whqsz/ExpressLRS_DIY_Hardware/link/mlrs_.png

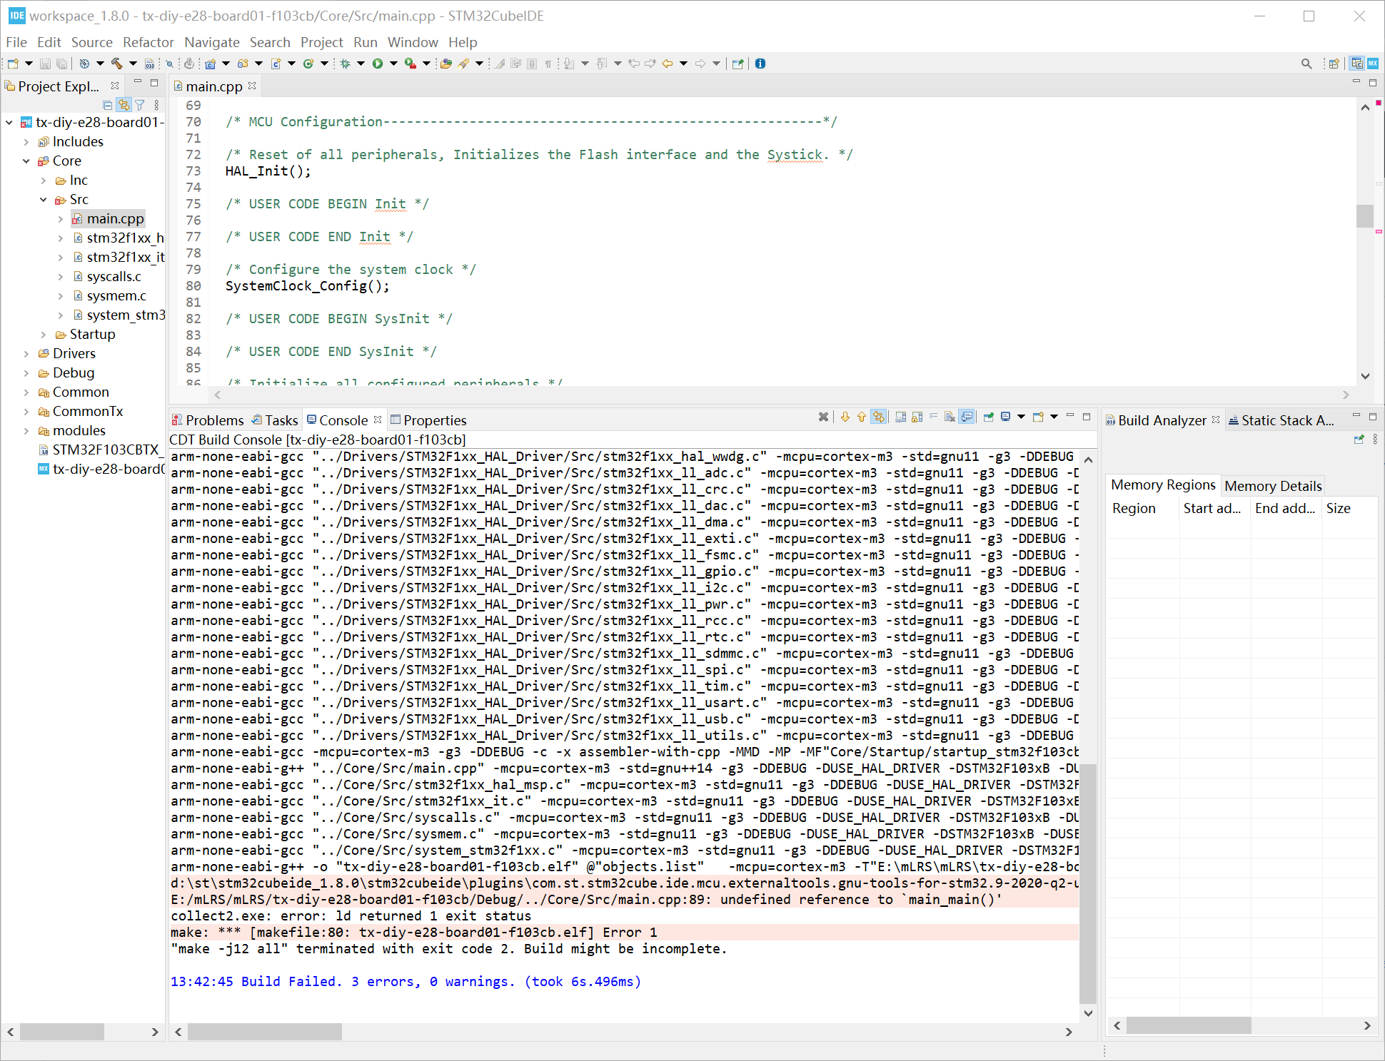
link/mlrs_.png
