whqsz/ExpressLRS_DIY_Hardware/RX-2G4-915M/2.4G/2.4_view.png

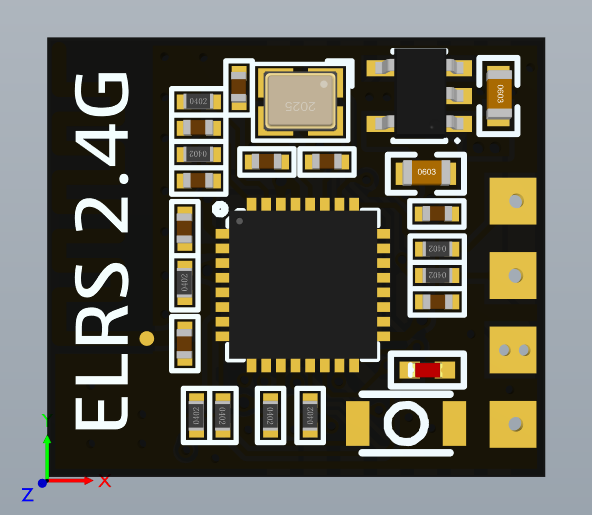
RX-2G4-915M/2.4G/2.4_view.png
