whqsz/ExpressLRS_DIY_Hardware/RX-2G4-915M/2.4G/焊接点位.png

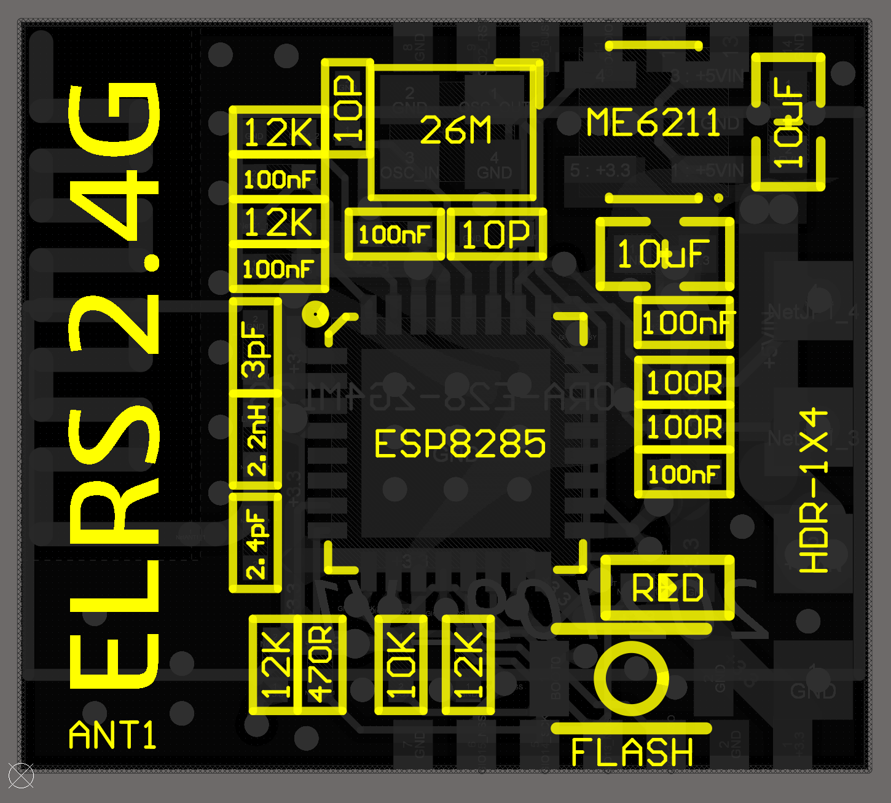
RX-2G4-915M/2.4G/焊接点位.png
