whqsz/ExpressLRS_DIY_Hardware/RX-2G4-915M/915M/E19-900M20S_ESP8285_CRSF_RX/915_view.png

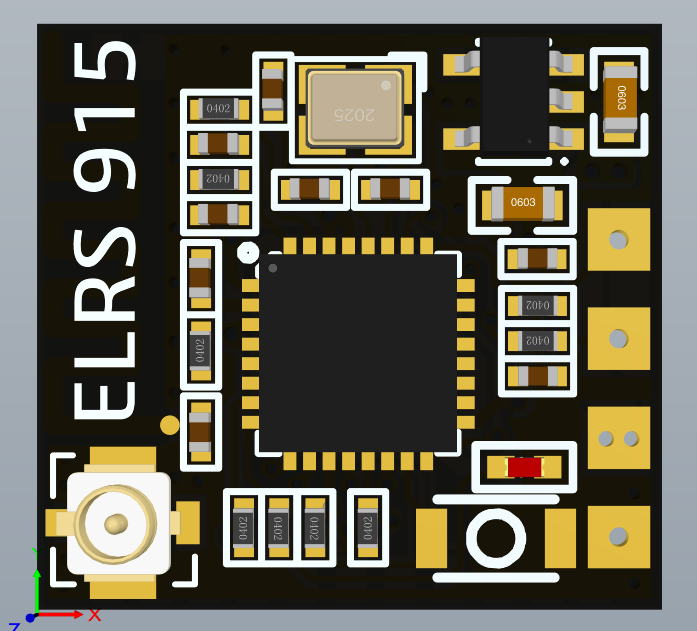
RX-2G4-915M/915M/E19-900M20S_ESP8285_CRSF_RX/915_view.png
