whqsz/ExpressLRS_DIY_Hardware/RX-2G4-915M/915M/E19-900M20S_ESP8285_PWM_RX/3D上.png

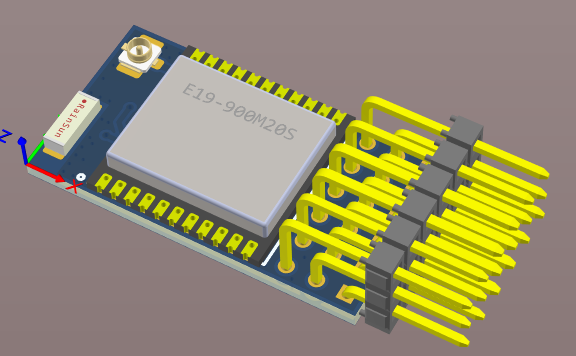
RX-2G4-915M/915M/E19-900M20S_ESP8285_PWM_RX/3D上.png
