whqsz/ExpressLRS_DIY_Hardware/RX-2G4-915M/915M/E32-900M20S_CRSF_RX/3D背.png

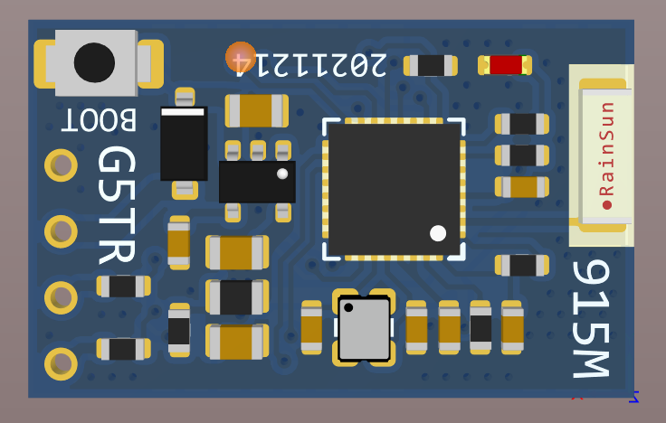
RX-2G4-915M/915M/E32-900M20S_CRSF_RX/3D背.png
