whqsz/ExpressLRS_DIY_Hardware/RX-2G4-915M/915M/E32-E900M20S_PWM_RX/3D正面.png

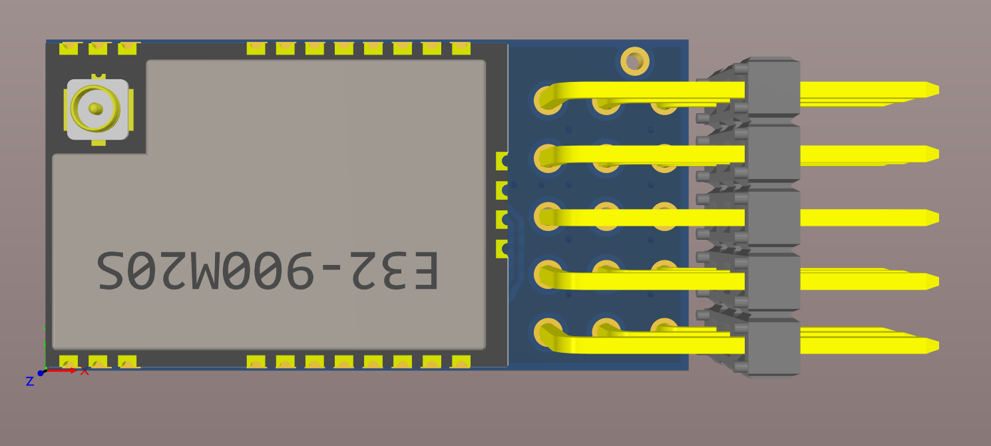
RX-2G4-915M/915M/E32-E900M20S_PWM_RX/3D正面.png
