whqsz/ExpressLRS_DIY_Hardware/TX/E19_915M_ESP32_2IN1_TX/2.4G模块引脚定义修改说明.png

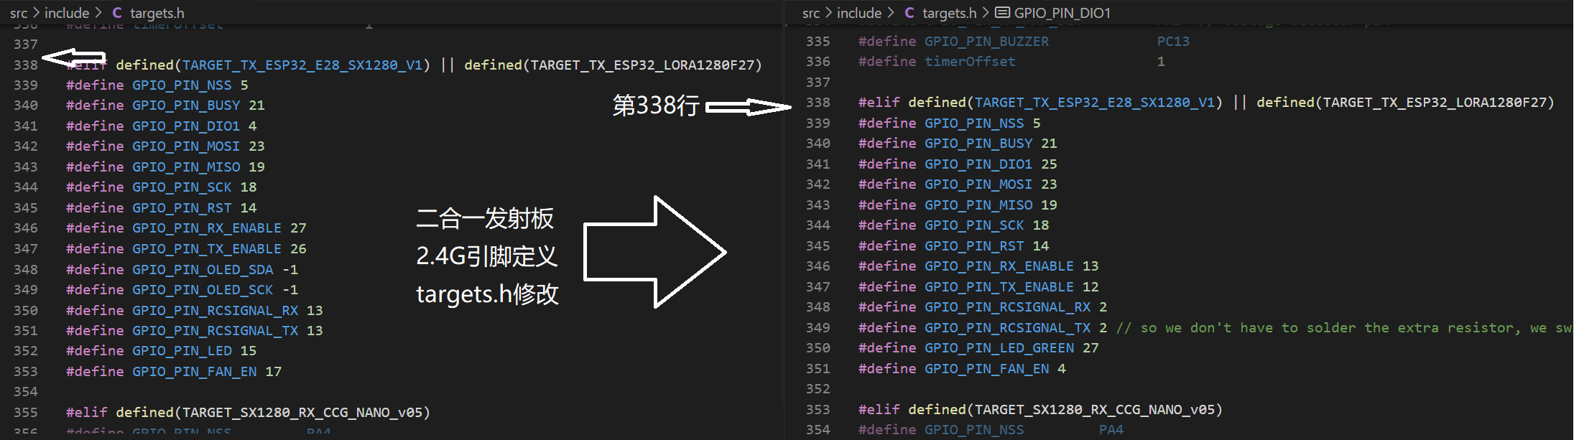
TX/E19_915M_ESP32_2IN1_TX/2.4G模块引脚定义修改说明.png
