whqsz/ExpressLRS_DIY_Hardware/TX/E19_915M_ESP32_2IN1_TX/3D背面.png

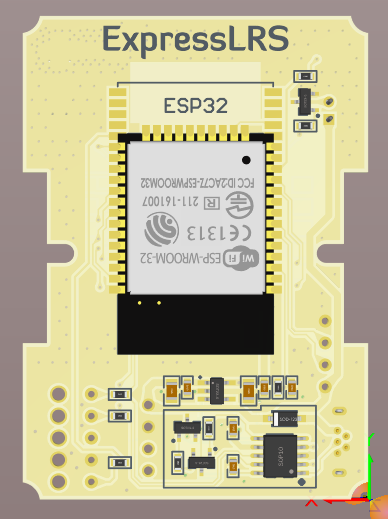
TX/E19_915M_ESP32_2IN1_TX/3D背面.png
