whqsz/ExpressLRS_DIY_Hardware/TX/E19_915M_ESP32_2IN1_TX/焊接点位正.png

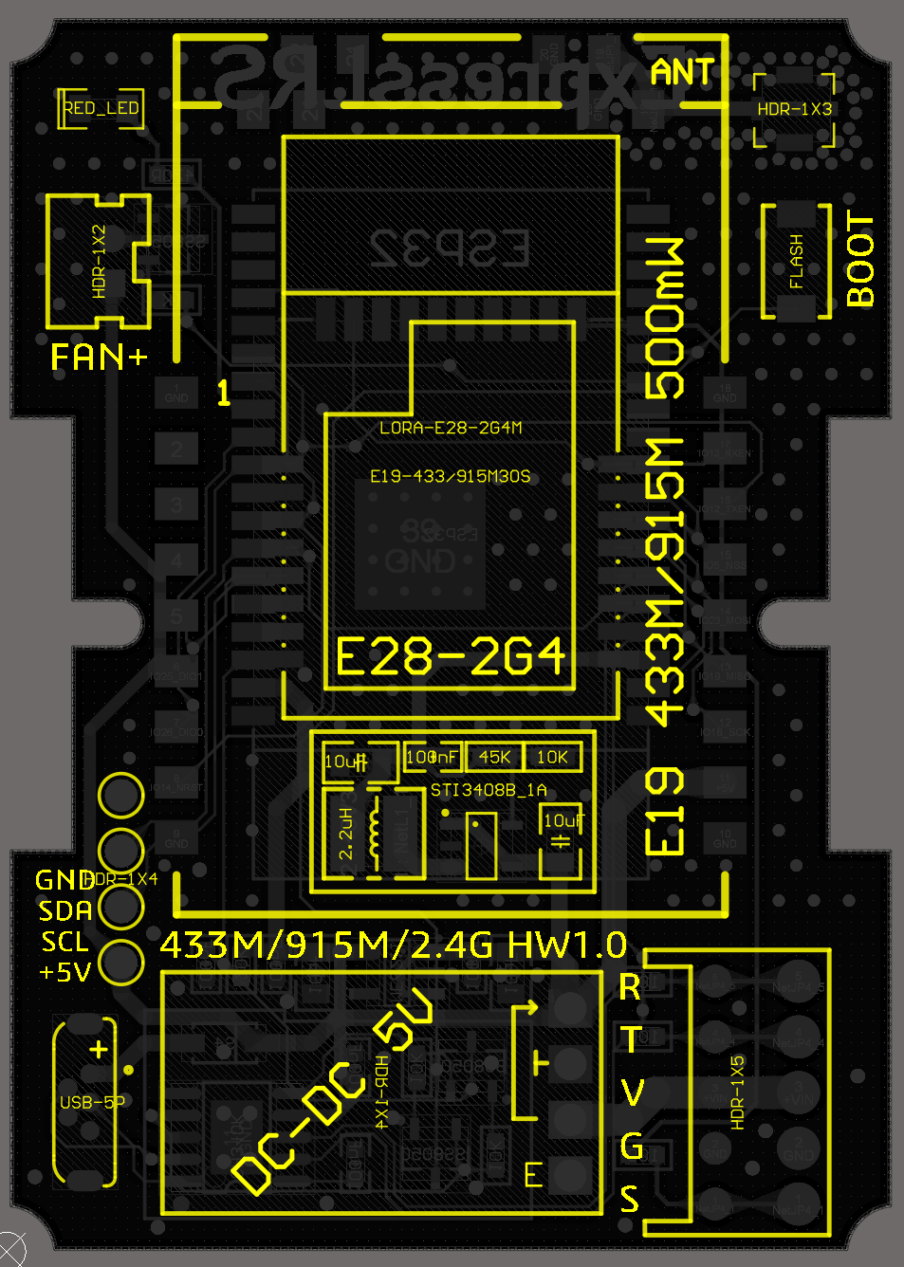
TX/E19_915M_ESP32_2IN1_TX/焊接点位正.png
