whqsz/ExpressLRS_DIY_Hardware/TX/E19_915M_ESP32_FULL_MODULE/3D前.png

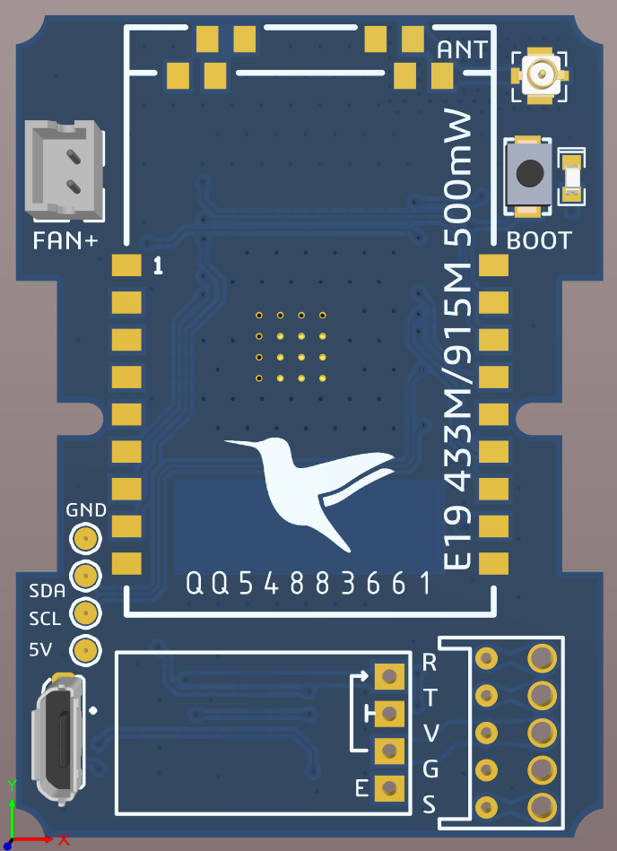
TX/E19_915M_ESP32_FULL_MODULE/3D前.png
