whqsz/ExpressLRS_DIY_Hardware/TX/E32_900M30S_TX/3D正面.png

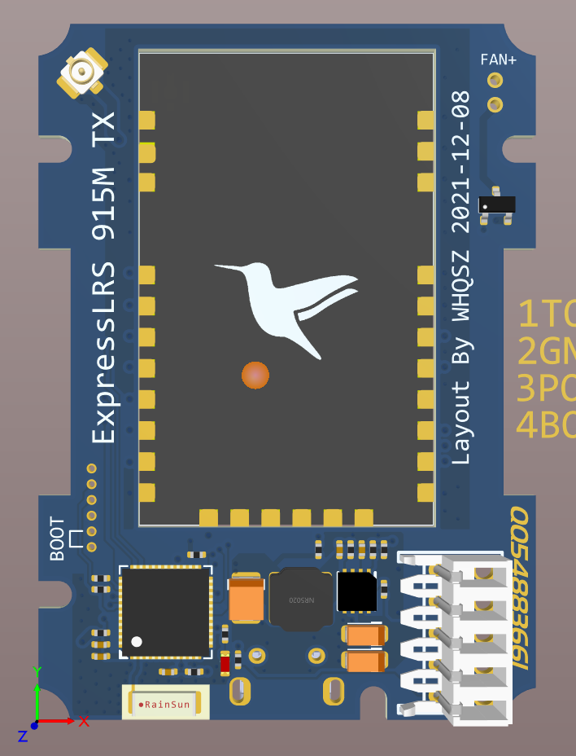
TX/E32_900M30S_TX/3D正面.png
